che711/signal-generator-esp32-ad9833/src/display.cpp

#include "display.h"

Display::Display()
    : _u8g2(U8G2_R0, U8X8_PIN_NONE, OLED_SCL_PIN, OLED_SDA_PIN)
{}

void Display::begin() {
    Wire.begin(OLED_SDA_PIN, OLED_SCL_PIN);
    // 400 kHz instead of the default 100: a full sendBuffer() frame takes
    // ~22 ms instead of ~90, blocking loop() far less
    _u8g2.setBusClock(400000);
    _u8g2.begin();
    _u8g2.setContrast(255);
    drawSplash();
    delay(1500);
}

void Display::drawSplash() {
    _u8g2.clearBuffer();
    _u8g2.setFont(u8g2_font_logisoso16_tr);
    _u8g2.drawStr(10, 28, "DDS GEN");
    _u8g2.setFont(u8g2_font_6x10_tf);
    _u8g2.drawStr(8, 44, "AD9833 + ESP32");
    _u8g2.drawStr(8, 58, "WiFi + NVS");
    _u8g2.sendBuffer();
}

void Display::drawConnecting(const String& ssid) {
    _u8g2.clearBuffer();
    _u8g2.setFont(u8g2_font_6x10_tf);
    _u8g2.drawStr(4, 14, "Connecting WiFi...");
    _u8g2.drawStr(4, 30, ssid.c_str());
    _u8g2.sendBuffer();
}

void Display::drawIP(const String& ip) {
    _u8g2.clearBuffer();
    _u8g2.setFont(u8g2_font_6x10_tf);
    _u8g2.drawStr(8, 14, "WiFi connected!");
    _u8g2.drawStr(8, 30, "Open browser:");
    _u8g2.drawStr(4, 48, ip.c_str());
    _u8g2.drawStr(4, 62, "dds-gen.local");
    _u8g2.sendBuffer();
}

// ── Layout 128×64 ─────────────────────────────────────────
//
//  px 0–12  ▌ WAVE: SINE          [W] ▌  ← inverted bar
//  px 13    ─────────────────────────── ← separator
//  px 14–34 ▌      1.000 kHz          ▌  ← logisoso16 (frequency)
//  px 35    ─────────────────────────── ← separator
//  px 36–44 ▌ STEP: 1kHz              ▌  ← 5x7
//  px 45–53 ▌ MyNetwork               ▌  ← 5x7 (SSID)
//  px 54–63 ▌ 192.168.1.45            ▌  ← 5x7 (IP)
//
void Display::drawMain(
    const String& freqStr,
    const char*   waveLabel,
    const char*   stepLabel,
    bool          wifiOn,
    const String& ssid,
    const String& ip)
{
    _u8g2.clearBuffer();

    // ── Top bar: WAVE + WiFi ──────────────────────────────
    _u8g2.setFont(u8g2_font_6x10_tf);
    _u8g2.setDrawColor(1);
    _u8g2.drawBox(0, 0, 128, 13);
    _u8g2.setDrawColor(0);
    _u8g2.drawStr(4, 10, "WAVE:");
    _u8g2.drawStr(36, 10, waveLabel);
    if (wifiOn) _u8g2.drawStr(107, 10, "[W]");
    _u8g2.setDrawColor(1);

    // ── Separator ─────────────────────────────────────────
    _u8g2.drawHLine(0, 13, 128);

    // ── Frequency: logisoso16, centered ───────────────────
    _u8g2.setFont(u8g2_font_logisoso16_tf);
    int fw = _u8g2.getStrWidth(freqStr.c_str());
    int fx = max(0, (128 - fw) / 2);
    _u8g2.drawStr(fx, 33, freqStr.c_str());

    // ── Separator ─────────────────────────────────────────
    _u8g2.drawHLine(0, 35, 128);

    // ── Three bottom lines: 5x7 ──────────────────────────
    _u8g2.setFont(u8g2_font_5x7_tf);

    // STEP
    _u8g2.drawStr(2, 44, "STP:");
    _u8g2.drawStr(24, 44, stepLabel);

    // SSID
    if (wifiOn && ssid.length() > 0) {
        _u8g2.drawStr(2, 53, "NET:");
        // Truncate the SSID if longer than 18 characters
        String s = ssid.length() > 18 ? ssid.substring(0, 18) : ssid;
        _u8g2.drawStr(24, 53, s.c_str());
    } else {
        _u8g2.drawStr(2, 53, "NET: --");
    }

    // IP
    if (wifiOn && ip.length() > 0) {
        _u8g2.drawStr(2, 62, "IP: ");
        _u8g2.drawStr(24, 62, ip.c_str());
    } else {
        _u8g2.drawStr(2, 62, "IP:  --");
    }

    _u8g2.sendBuffer();
}
