che711/signal-generator-esp32-ad9833/src/display.h

#pragma once

#include <Arduino.h>
#include <U8g2lib.h>
#include <Wire.h>
#include "config.h"

class Display {
public:
    Display();
    void begin();

    void drawMain(
        const String& freqStr,
        const char*   waveLabel,
        const char*   stepLabel,
        bool          wifiOn = false,
        const String& ssid   = "",
        const String& ip     = ""
    );

    void drawIP(const String& ip);
    void drawSplash();

    // WiFi status screen, does not redraw the frequency
    void drawConnecting(const String& ssid);

private:
    U8G2_SSD1306_128X64_NONAME_F_HW_I2C _u8g2;
};
